waicool20/LaserScanningProjector/Software/src/main.h

#pragma once

enum struct render {
  NONE,
  BASIC_TUPLE,
  BASIC_RECT,
  BASIC_BITMAP,
  DEBUG_HOME_LASER,
  INIT_HOME_LASER,
  AUDIO_MIC,
  USB,
  DEBUG_MANUAL,
  AUDIO_HEADPHONES,
  AUDIO_HEADPHONES_XY
};

extern render rendering;
